sharpie7/pico-pattern/photos/img1.jpg

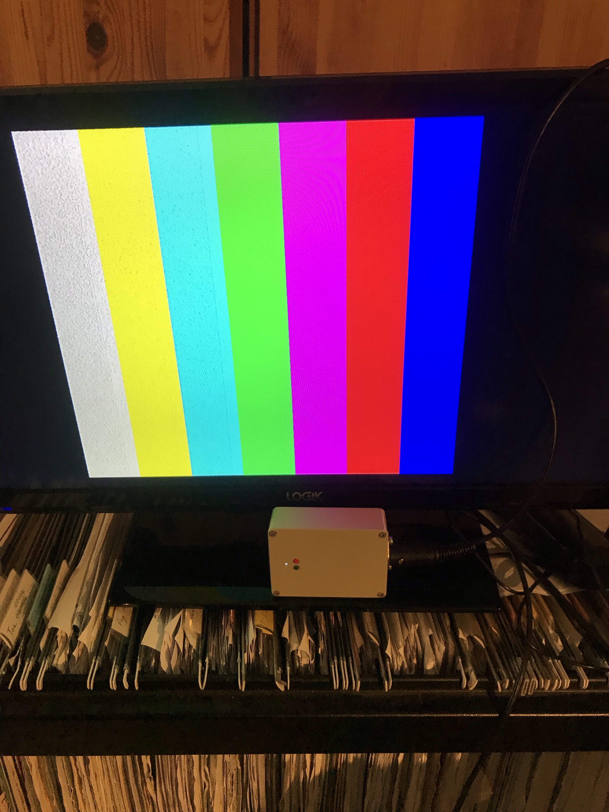
photos/img1.jpg
